popqq/Smart_Plant/docs/source/_static/Slide 1.png

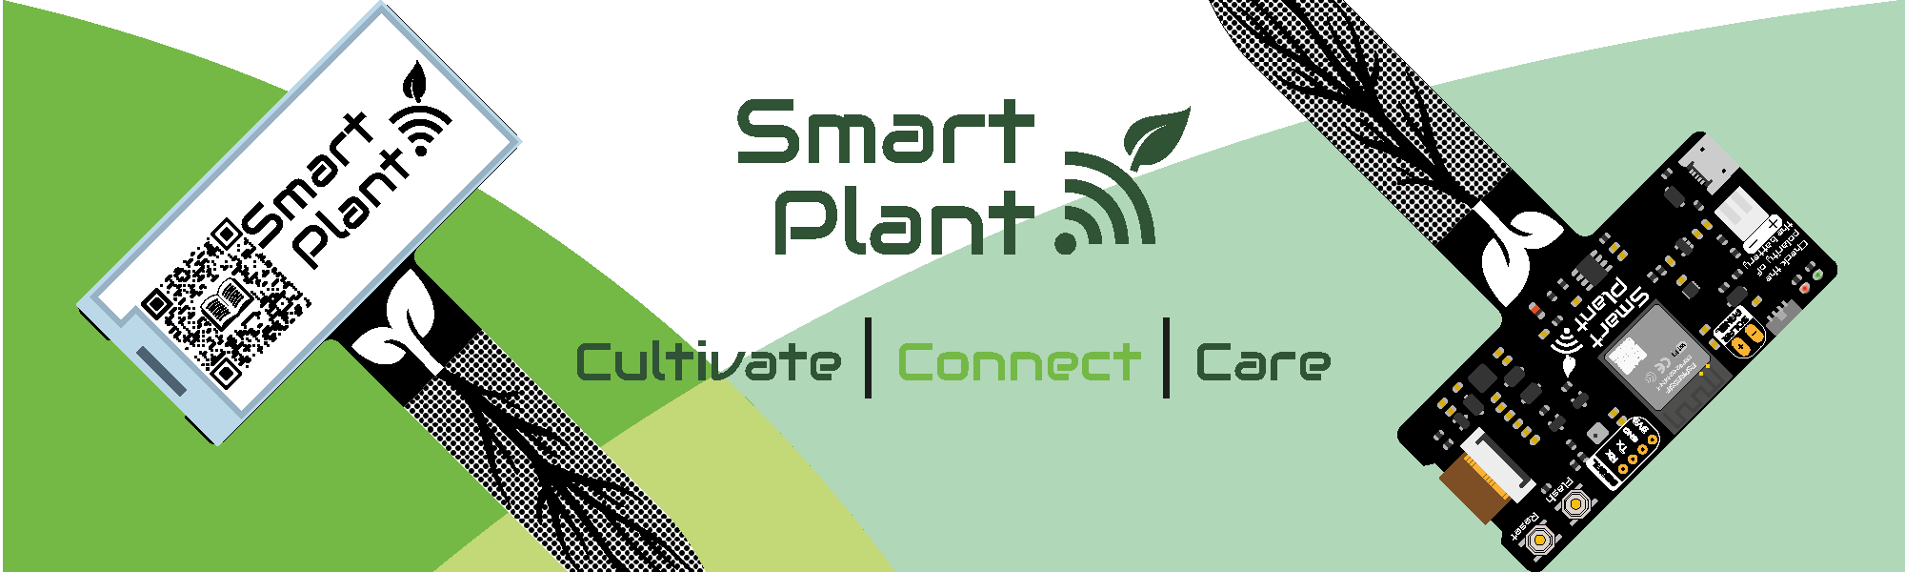
docs/source/_static/Slide 1.png
