popqq/Smart_Plant/docs/source/_static/Slide 3.png

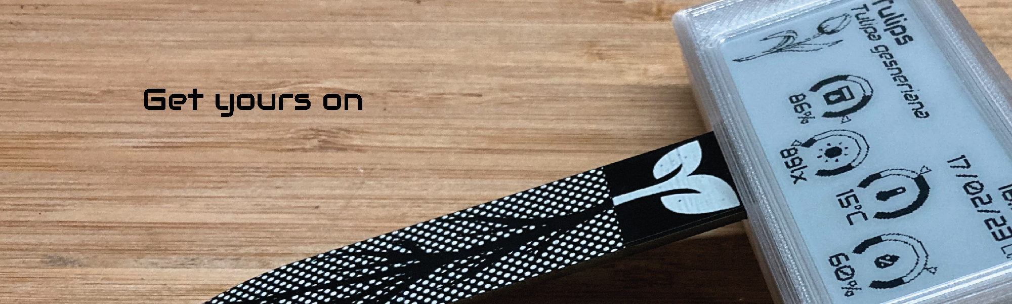
docs/source/_static/Slide 3.png
