popqq/Smart_Plant/Documentation/Silkscreen/Bottom.bmp

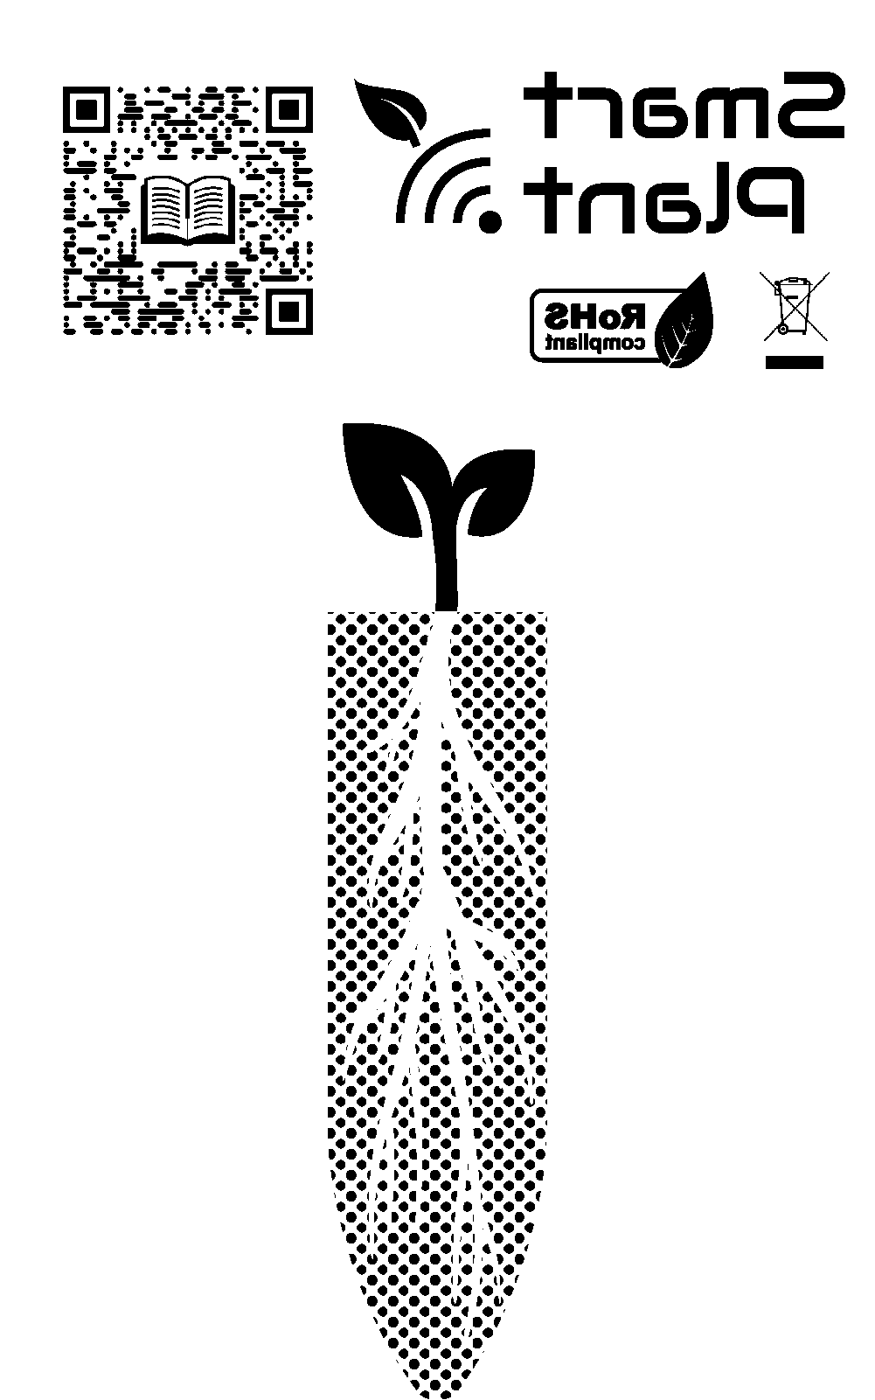
Documentation/Silkscreen/Bottom.bmp
