popqq/Smart_Plant/Documentation/Silkscreen/Top.bmp

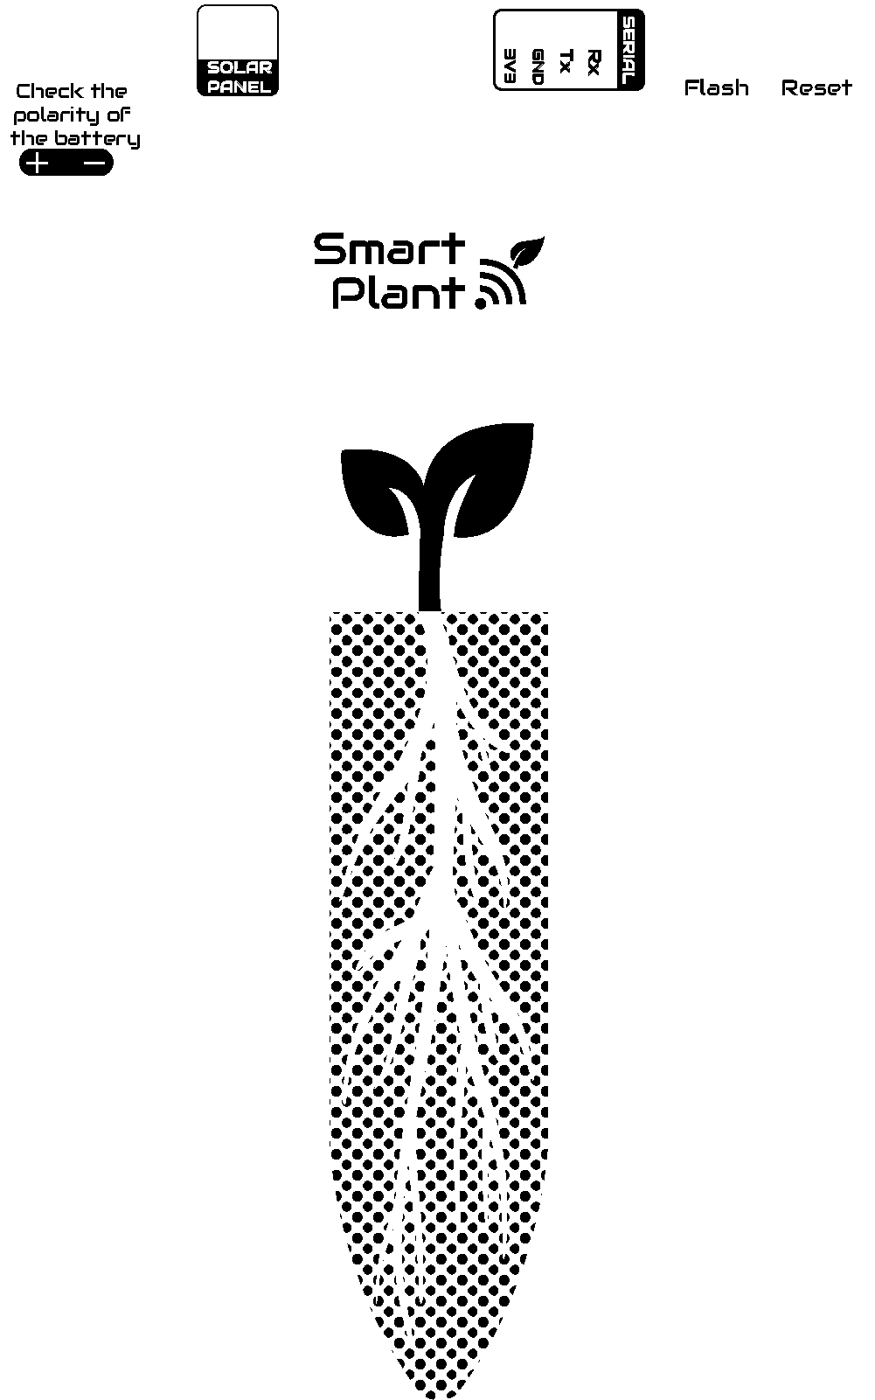
Documentation/Silkscreen/Top.bmp
